stagehandshawn/EvoCmdWing/Cad_models/V0.2/stls/small_encoder_mount.stl

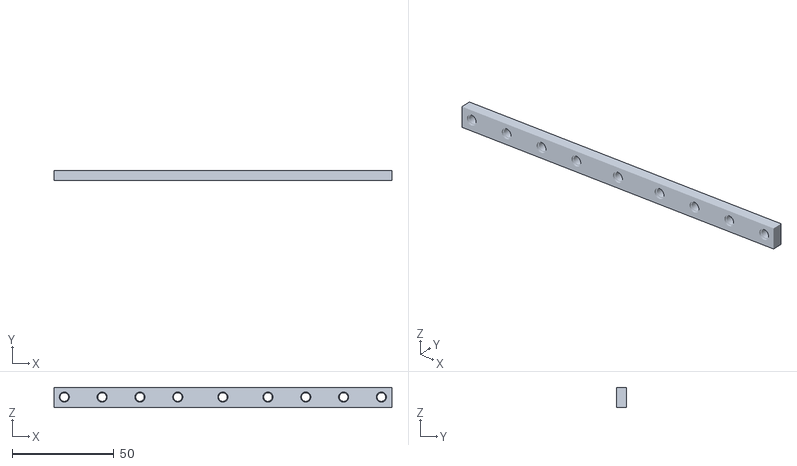
[picture p23: CAD file, 2025-07-23]
Cad_models/V0.2/stls/small_encoder_mount.stl
166.0 x 5.00 x 10.0
