stagehandshawn/EvoCmdWing/Cad_models/V0.2/stls/encoder_flip_button_soild_no_led.stl

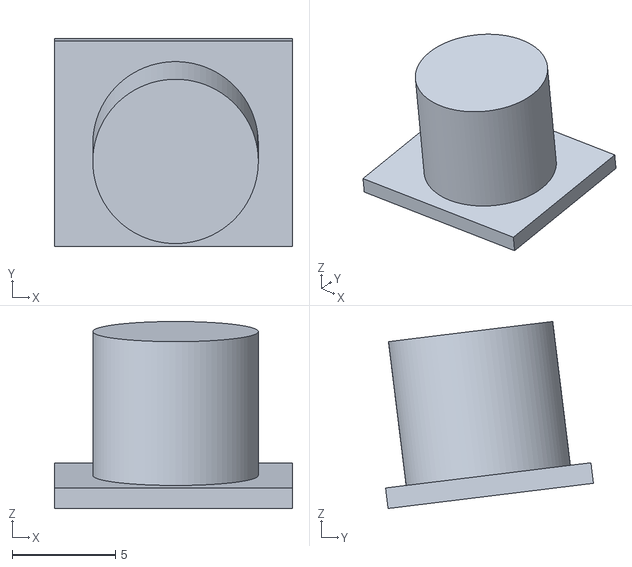
[picture p24: CAD file, 2025-07-23]
Cad_models/V0.2/stls/encoder_flip_button_soild_no_led.stl
11.5 x 10.0 x 9.04
