stagehandshawn/EvoCmdWing/Cad_models/V0.2/stls/encoder_wheel.stl

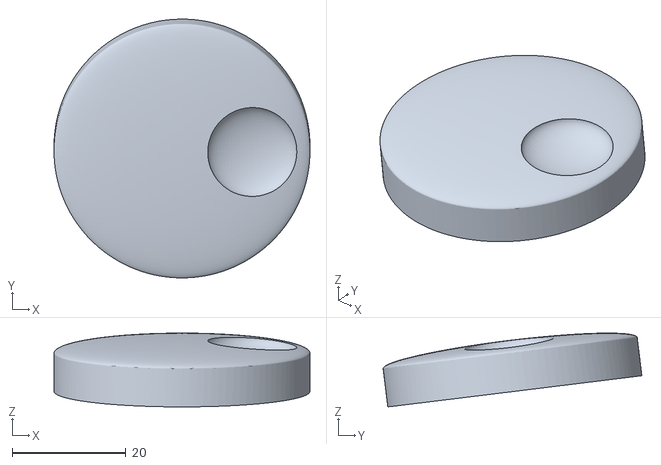
[picture p25: CAD file, 2025-07-23]
Cad_models/V0.2/stls/encoder_wheel.stl
45.0 x 45.5 x 13.0
