stagehandshawn/EvoCmdWing/Cad_models/V0.1/stls/Keyplate.stl

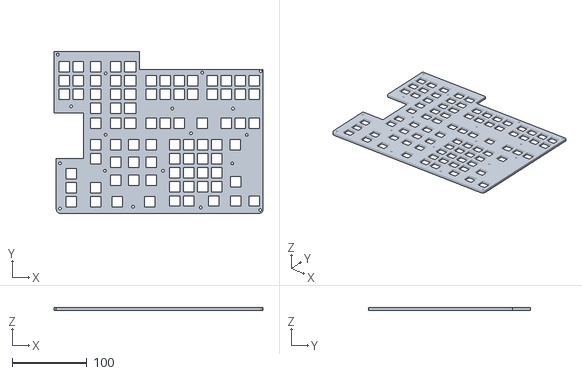
[picture p26: CAD file, 2025-06-17, an earlier design]
Cad_models/V0.1/stls/Keyplate.stl
278.9 x 215.8 x 4.00
