stagehandshawn/EvoCmdWing/help_files/EvoCmgWing_keyplate_wiring_diagram.png

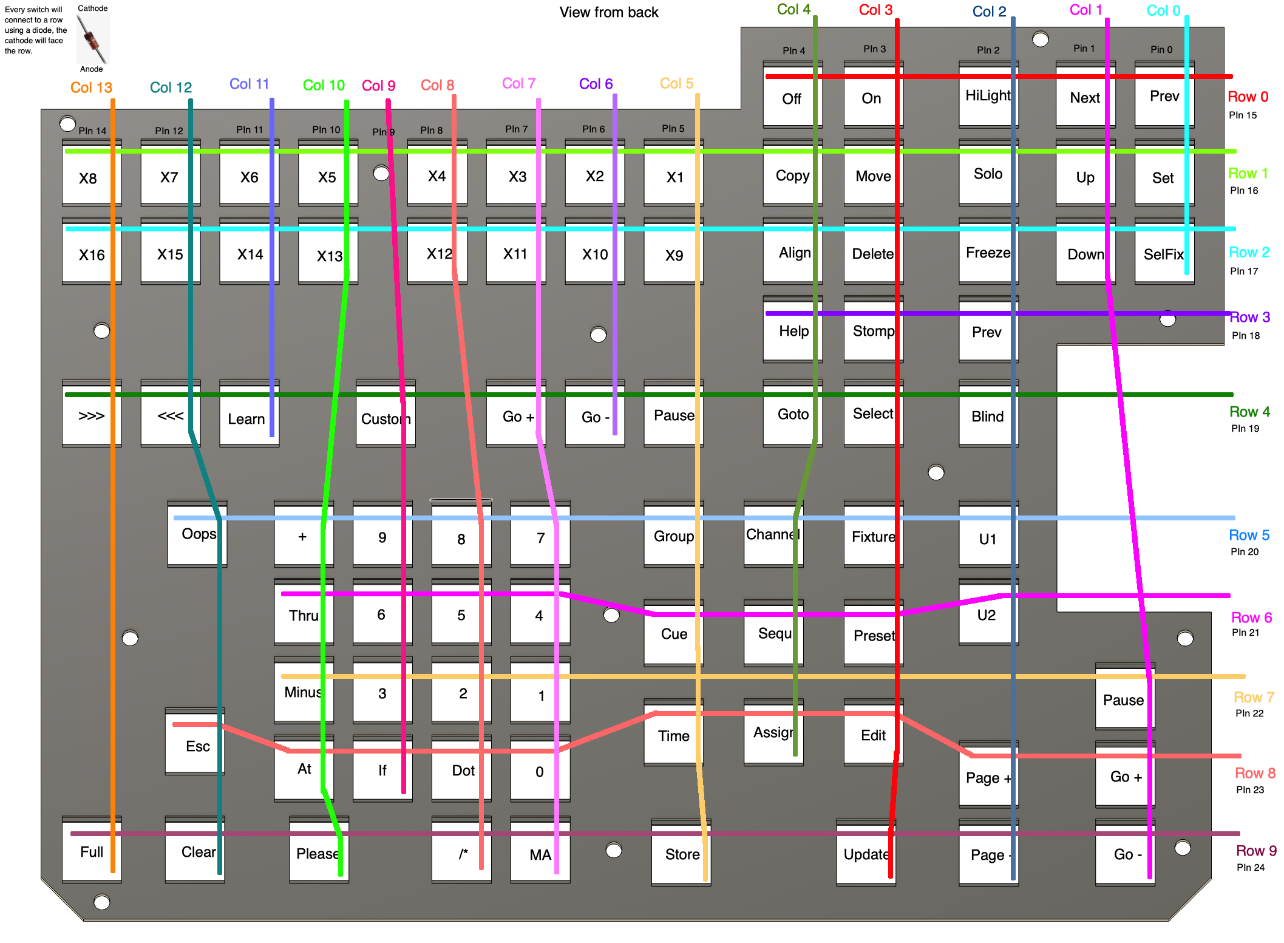
help_files/EvoCmgWing_keyplate_wiring_diagram.png
