stagehandshawn/EvoCmdWing/help_files/XKey_MidiRemote_setup_populated.png

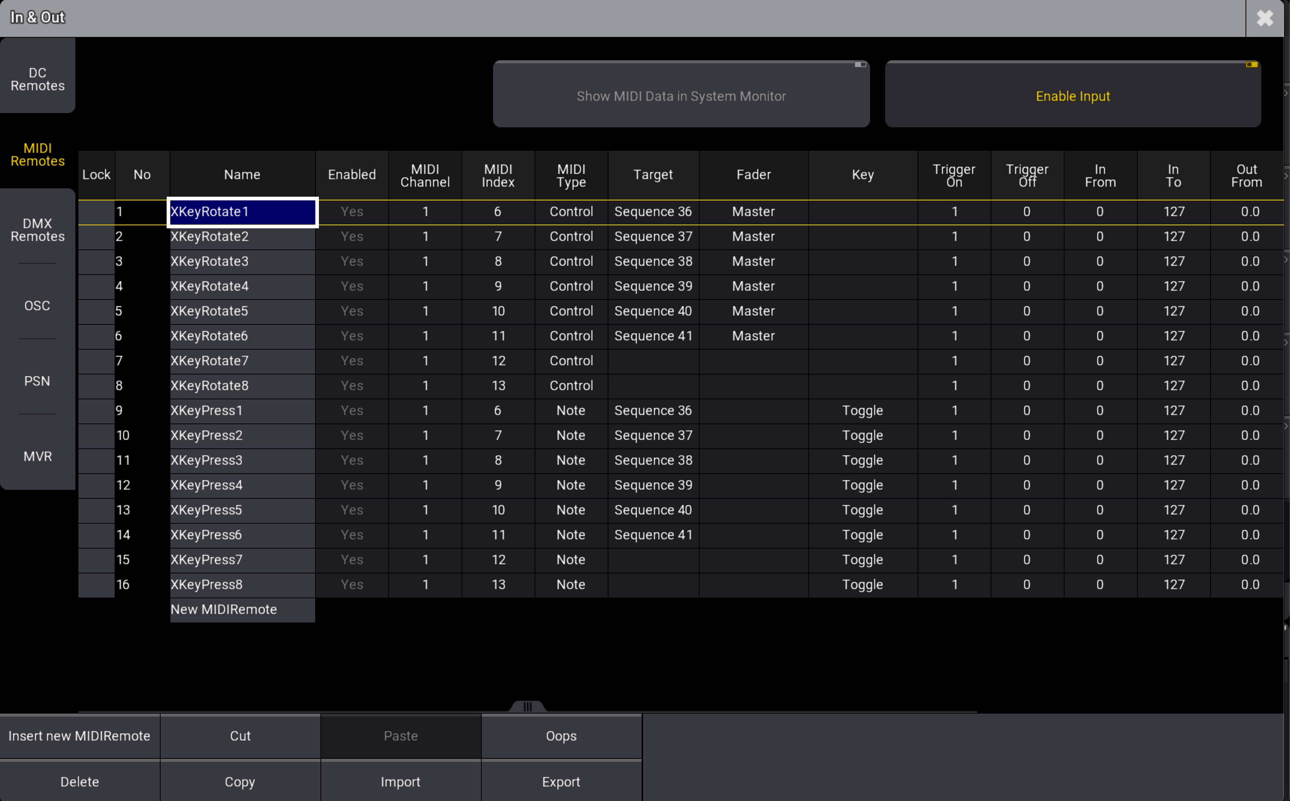
help_files/XKey_MidiRemote_setup_populated.png
