stagehandshawn/EvoCmdWing/images/matrix_wiring_1.jpg

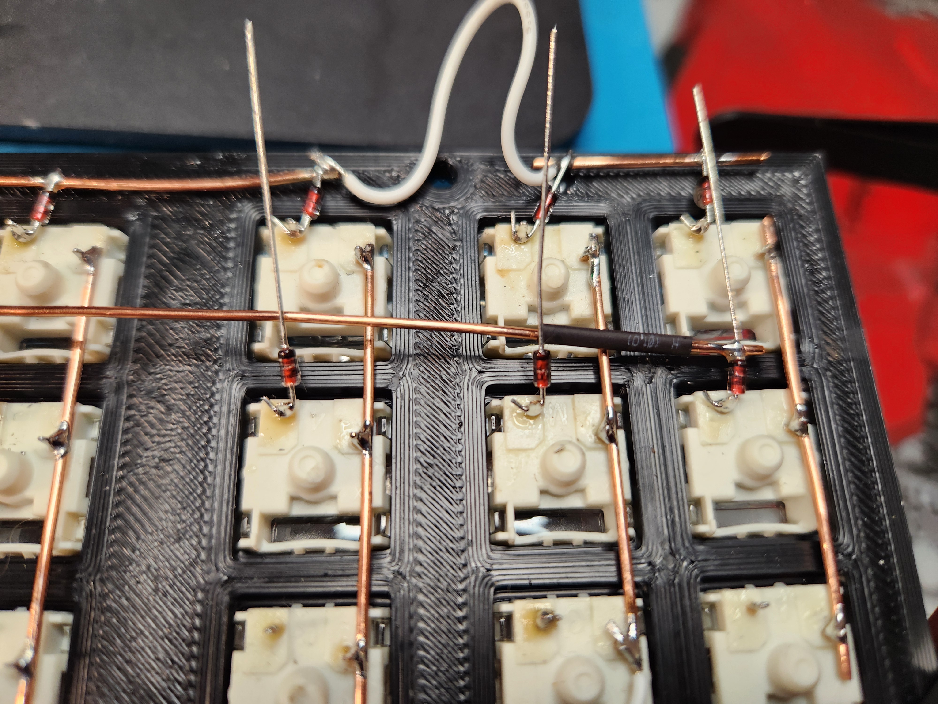
images/matrix_wiring_1.jpg
