stagehandshawn/EvoCmdWing/images/matrix_wiring_2.jpg

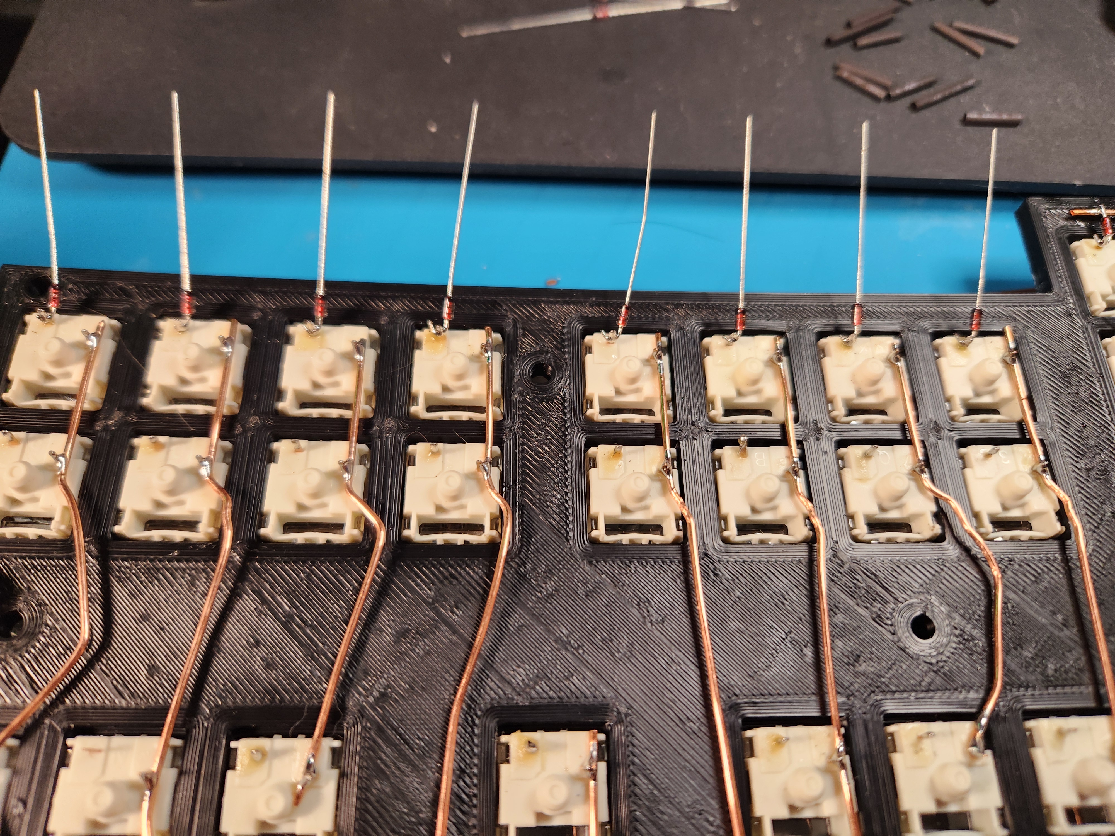
images/matrix_wiring_2.jpg
