stagehandshawn/EvoCmdWing/images/matrix_wiring_0.jpg

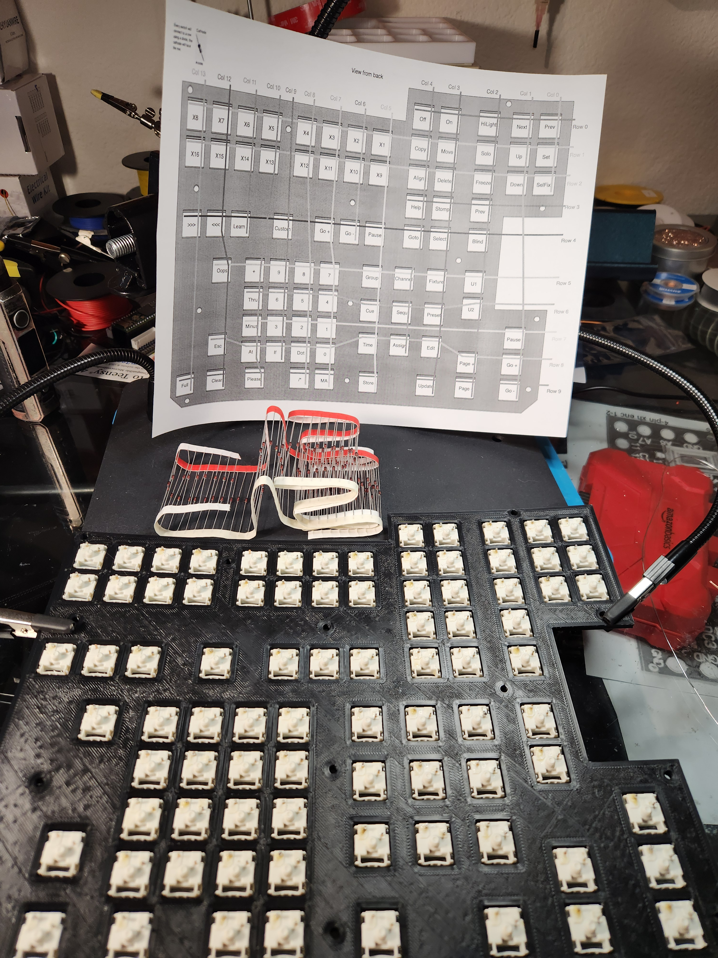
images/matrix_wiring_0.jpg
